dancard32/spotify-player/assets/Blank_3D_Render.png

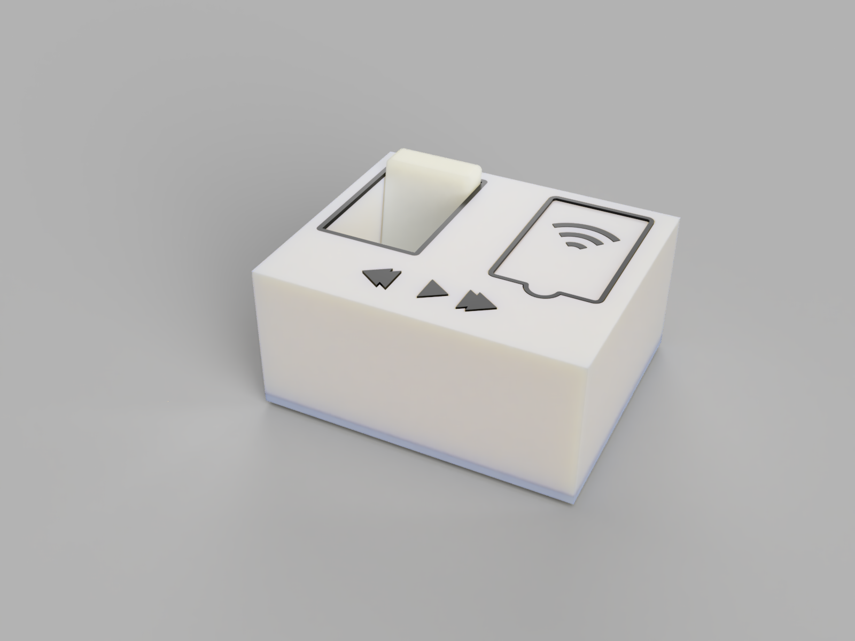
assets/Blank_3D_Render.png
