dancard32/spotify-player/assets/coverPhoto.png

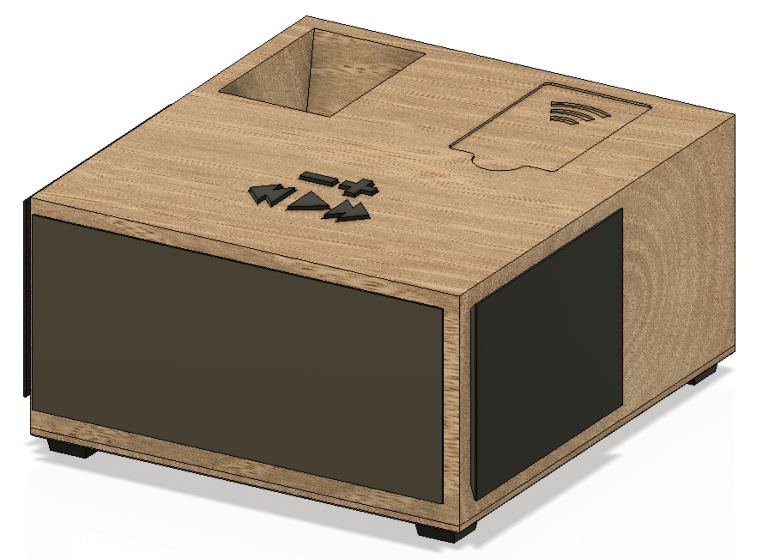
assets/coverPhoto.png
