dancard32/spotify-player/images/cards/cover_art/.png

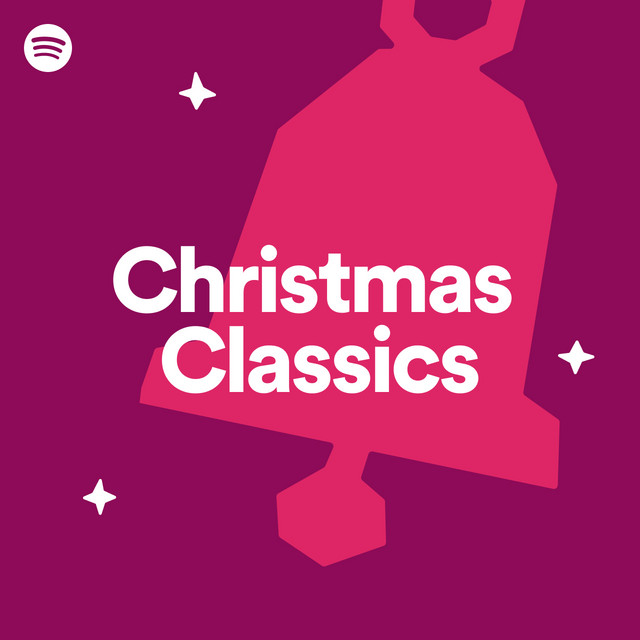
images/cards/cover_art/.png
