dancard32/spotify-player/images/cards/cover_art/African Heat.png

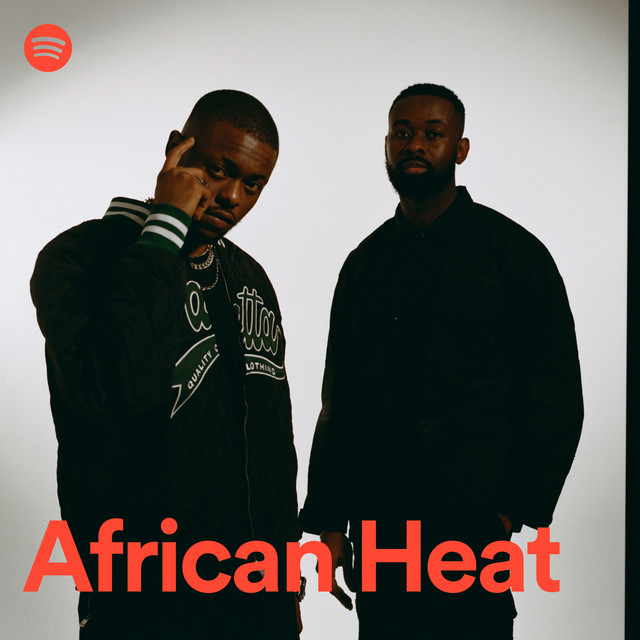
images/cards/cover_art/African Heat.png
