dancard32/spotify-player/images/cards/cover_art/All Out 60s.png

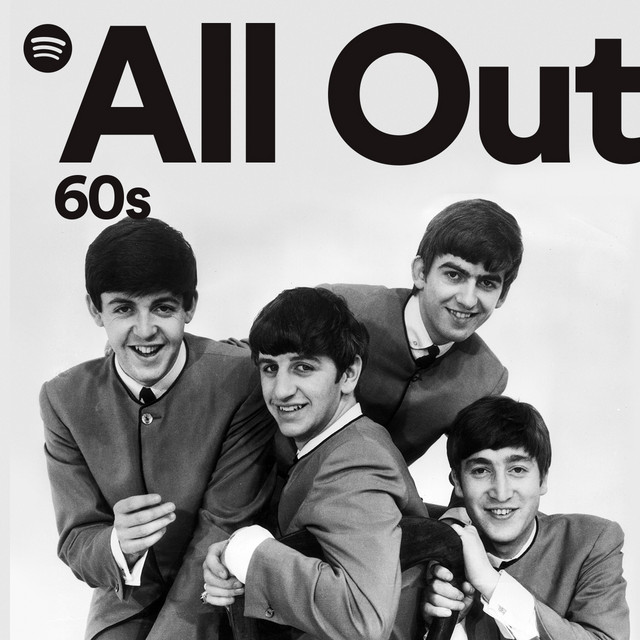
images/cards/cover_art/All Out 60s.png
