dancard32/spotify-player/images/cards/cover_art/All Out 70s.png

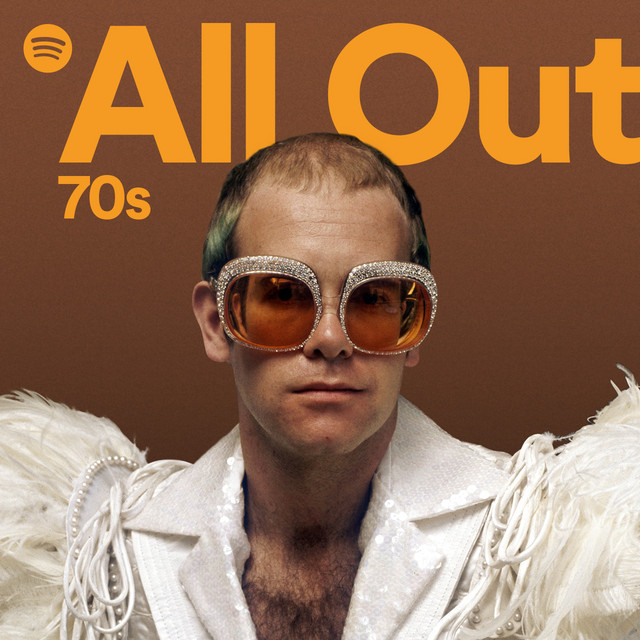
images/cards/cover_art/All Out 70s.png
