dancard32/spotify-player/images/cards/cover_art/All Out 90s.png

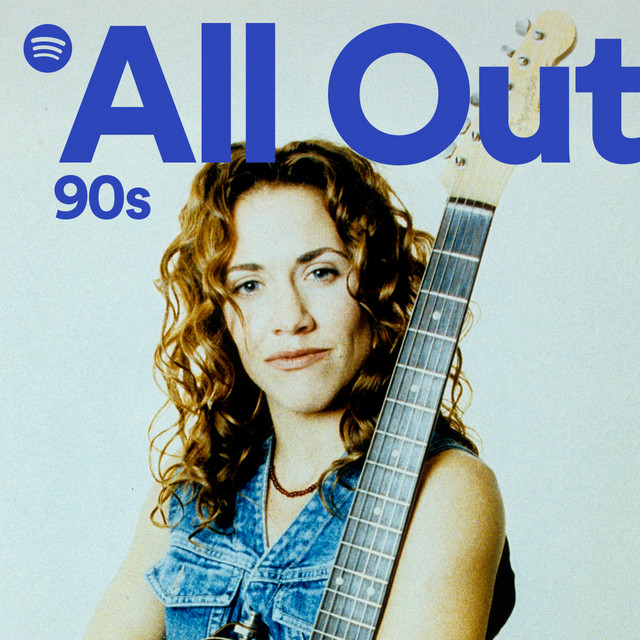
images/cards/cover_art/All Out 90s.png
