dancard32/spotify-player/images/cards/cover_art/All Out 2000s.png

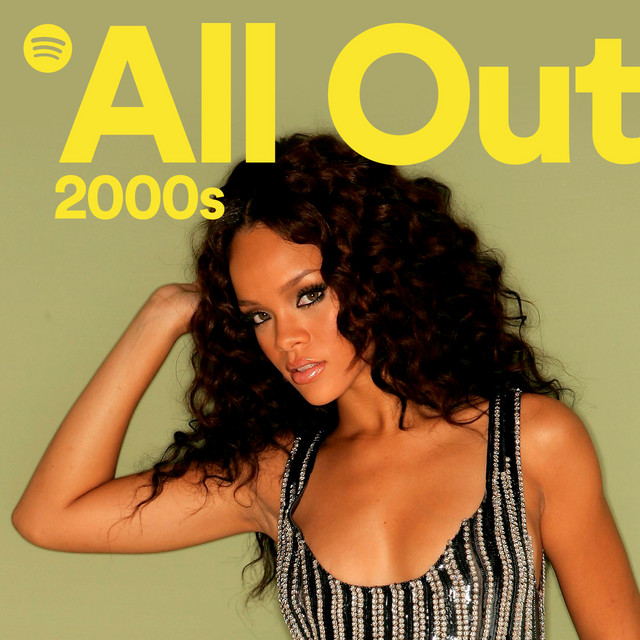
images/cards/cover_art/All Out 2000s.png
