dancard32/spotify-player/images/cards/cover_art/Atmospheric Sci-Fi.png

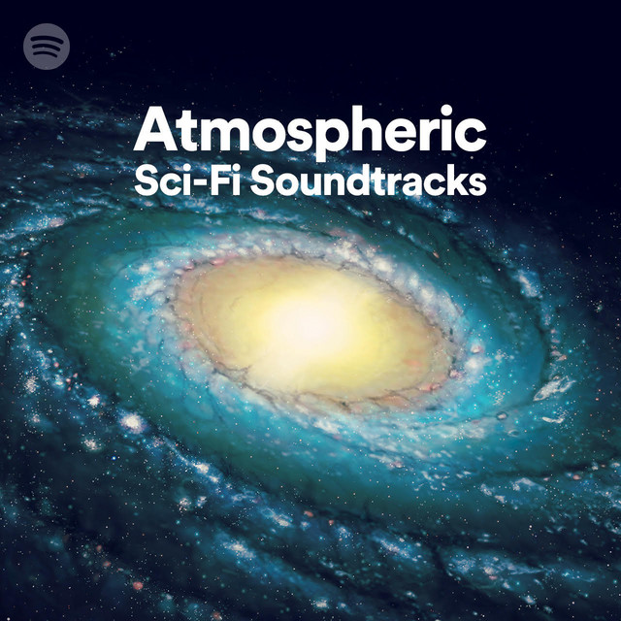
images/cards/cover_art/Atmospheric Sci-Fi.png
