dancard32/spotify-player/images/cards/cover_art/Chilled R&B.png

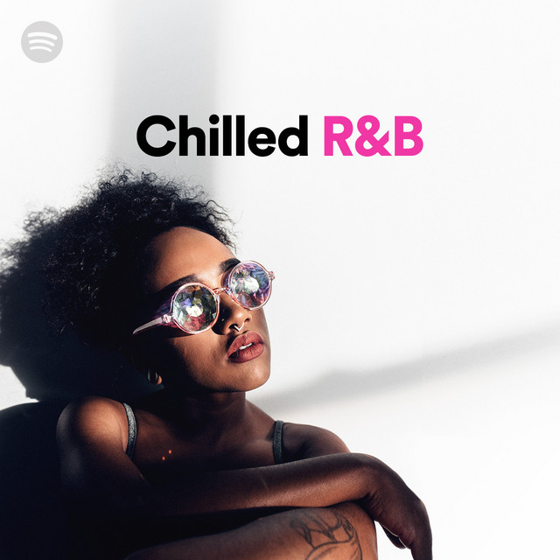
images/cards/cover_art/Chilled R&B.png
