dancard32/spotify-player/images/cards/cover_art/Country .png

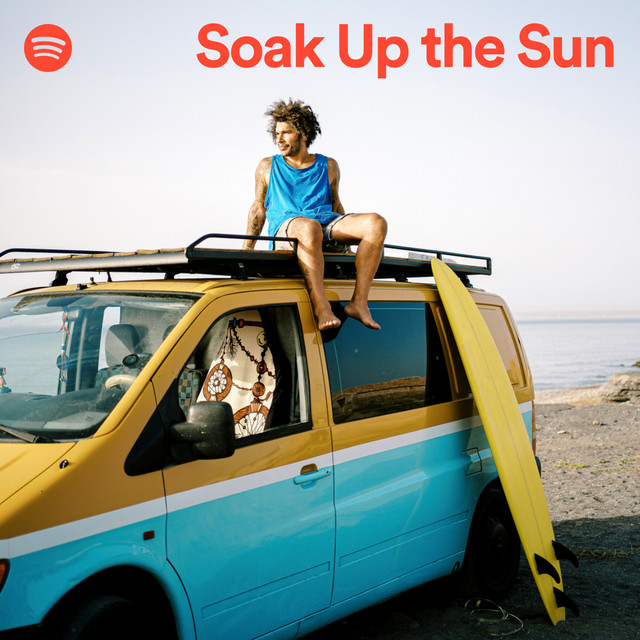
images/cards/cover_art/Country .png
