dancard32/spotify-player/images/cards/cover_art/Funk Outta Here.png

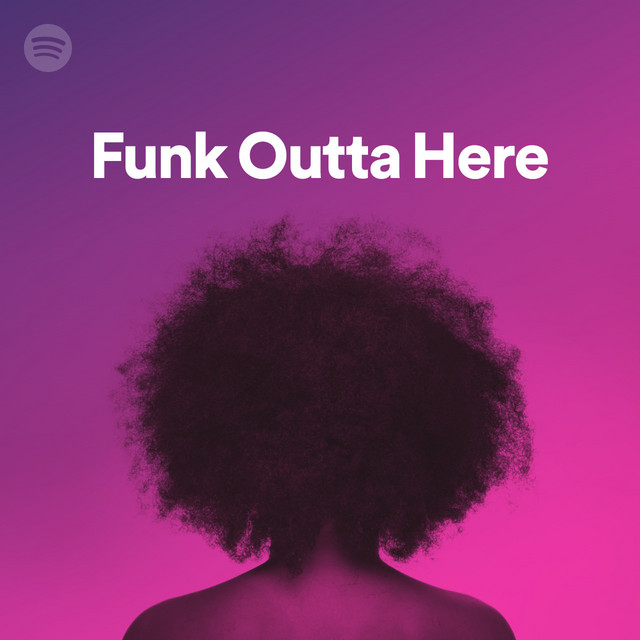
images/cards/cover_art/Funk Outta Here.png
