dancard32/spotify-player/images/cards/cover_art/Hip Hop Mix.png

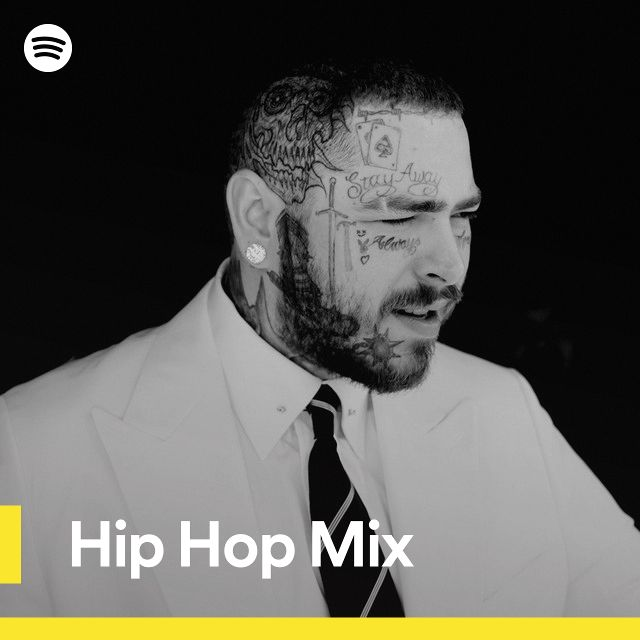
images/cards/cover_art/Hip Hop Mix.png
