dancard32/spotify-player/images/cards/cover_art/Kurzgesagt in a nutshell.png

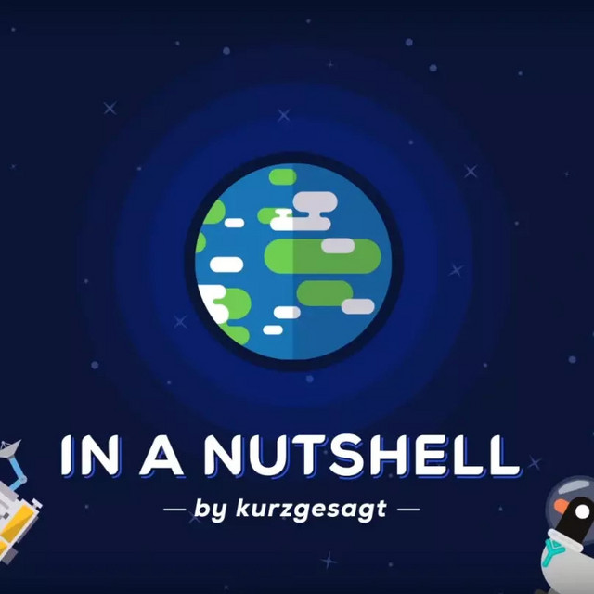
images/cards/cover_art/Kurzgesagt in a nutshell.png
