dancard32/spotify-player/images/cards/cover_art/Late Night Jazz.png

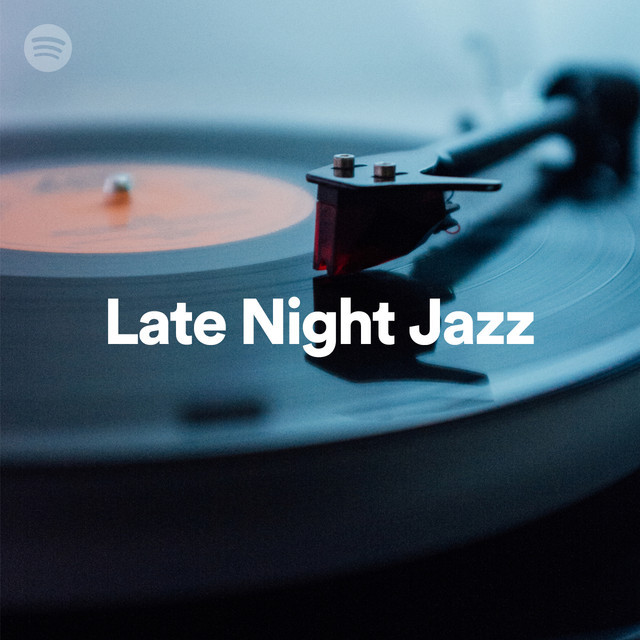
images/cards/cover_art/Late Night Jazz.png
