dancard32/spotify-player/images/cards/cover_art/lofi hip hop music.png

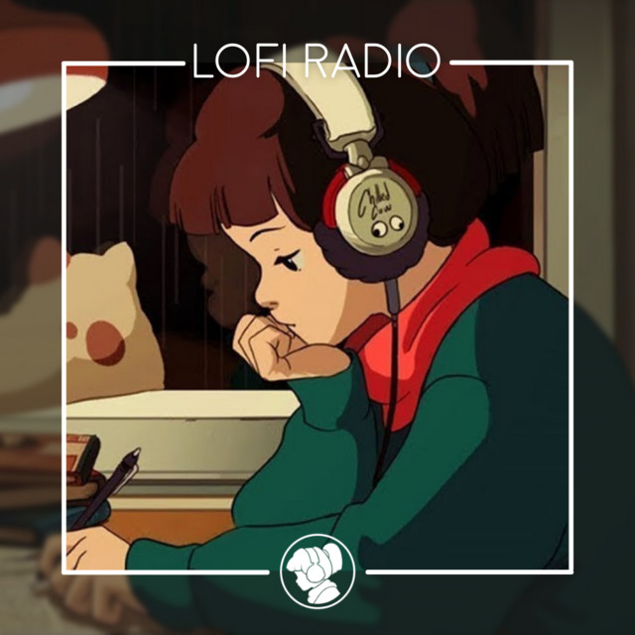
images/cards/cover_art/lofi hip hop music.png
