dancard32/spotify-player/images/cards/cover_art/New Music Friday.png

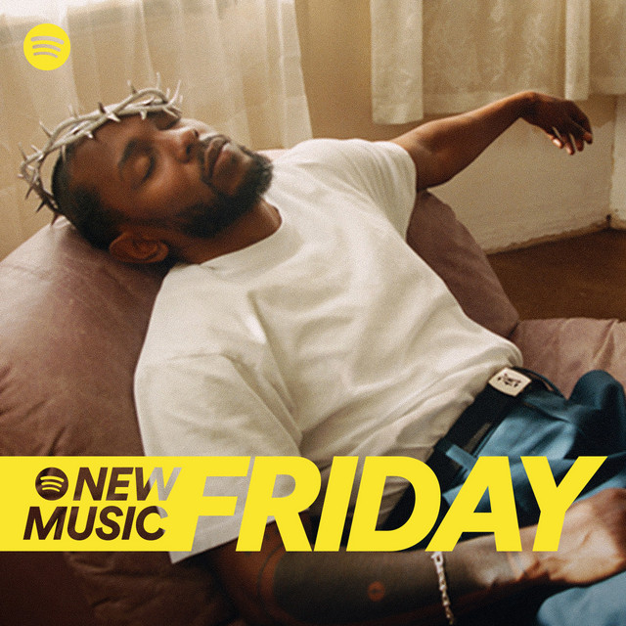
images/cards/cover_art/New Music Friday.png
