dancard32/spotify-player/images/cards/cover_art/Party Mix.png

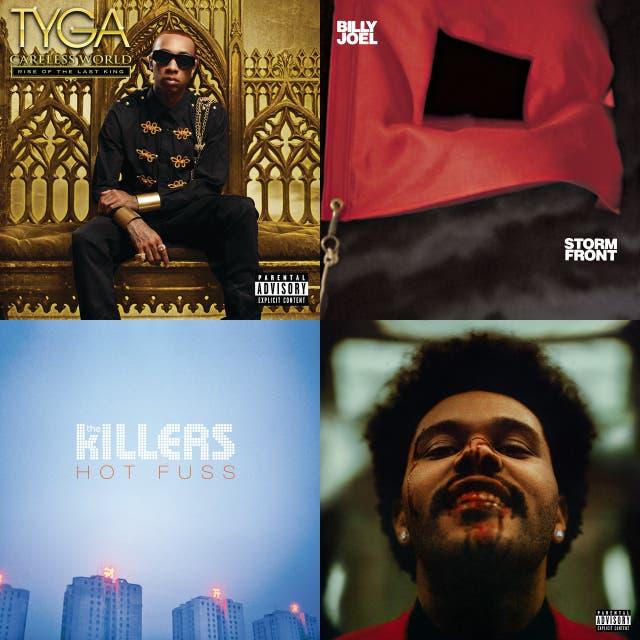
images/cards/cover_art/Party Mix.png
