dancard32/spotify-player/images/cards/cover_art/R&B Mix.png

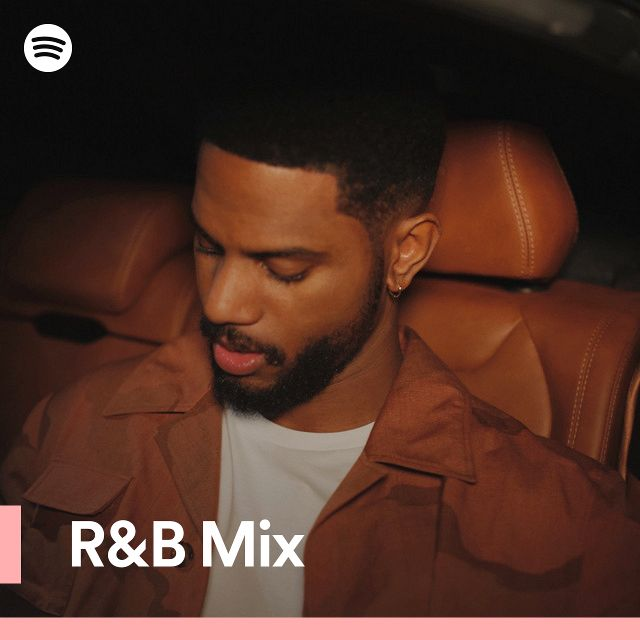
images/cards/cover_art/R&B Mix.png
