dancard32/spotify-player/images/cards/cover_art/Rap.png

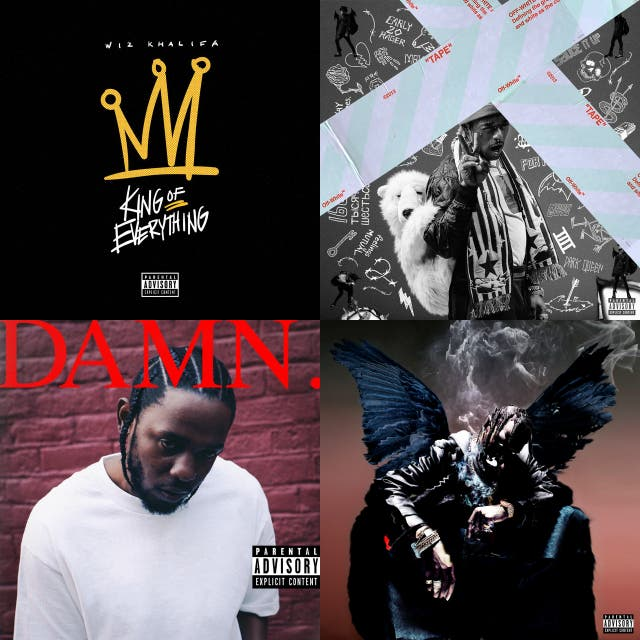
images/cards/cover_art/Rap.png
