dancard32/spotify-player/images/cards/cover_art/RapCaviar.png

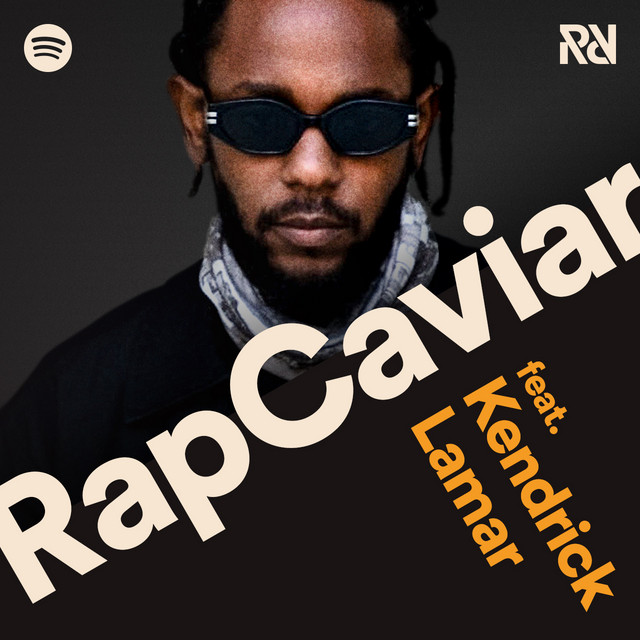
images/cards/cover_art/RapCaviar.png
