dancard32/spotify-player/images/cards/cover_art/Road Trips.png

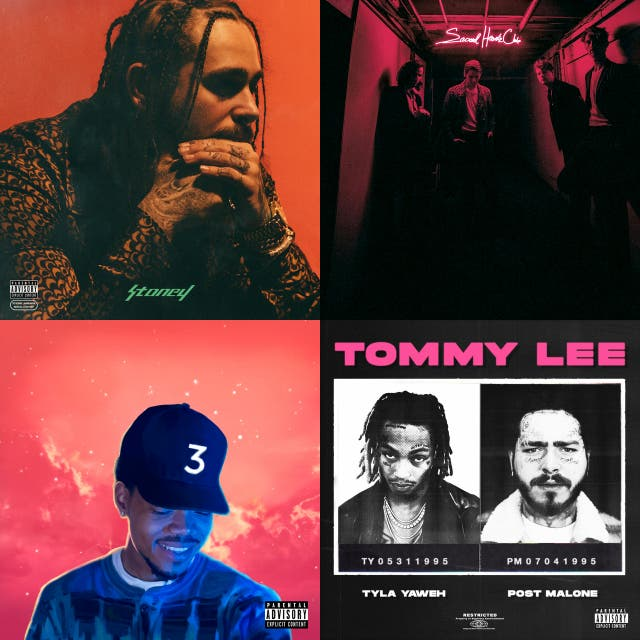
images/cards/cover_art/Road Trips.png
