dancard32/spotify-player/images/cards/cover_art/Rock Classics.png

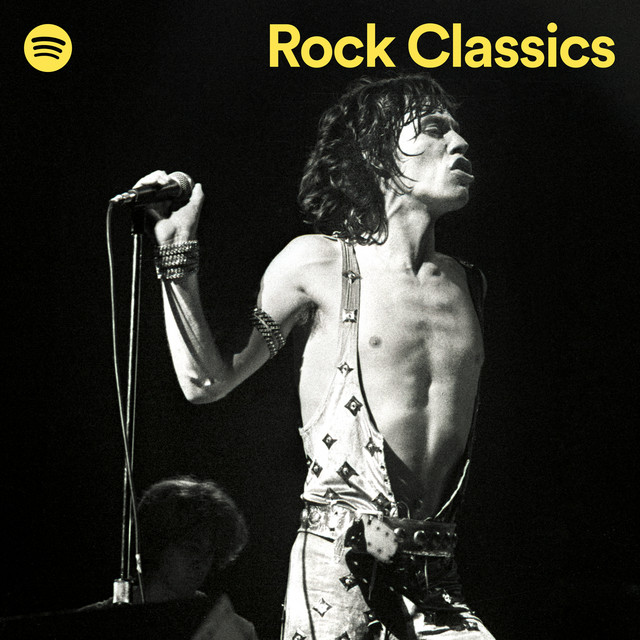
images/cards/cover_art/Rock Classics.png
