dancard32/spotify-player/images/cards/cover_art/Rock Party.png

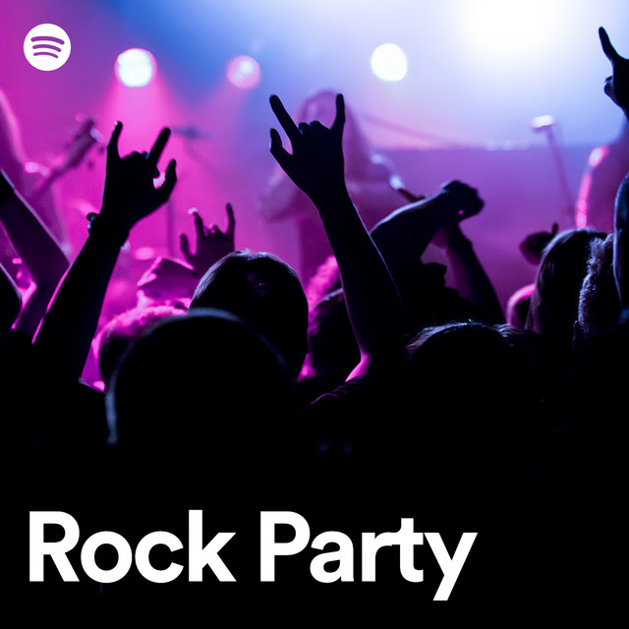
images/cards/cover_art/Rock Party.png
