dancard32/spotify-player/images/cards/cover_art/Soft Pop Hits.png

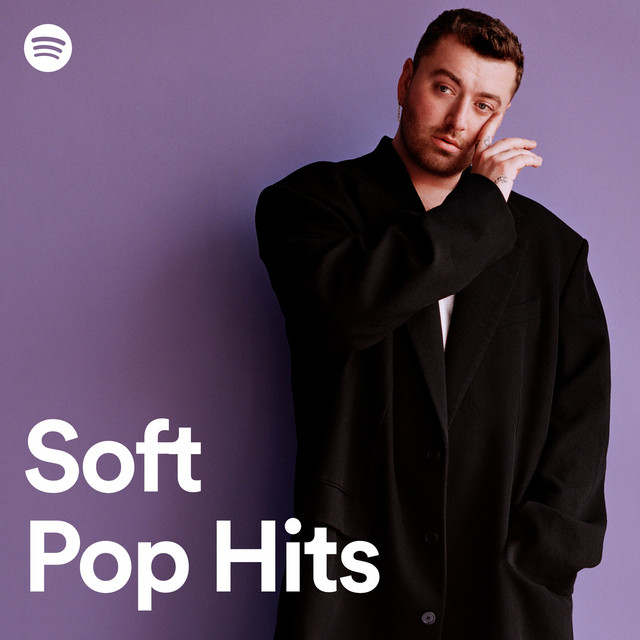
images/cards/cover_art/Soft Pop Hits.png
