dancard32/spotify-player/images/cards/cover_art/Soul Revived.png

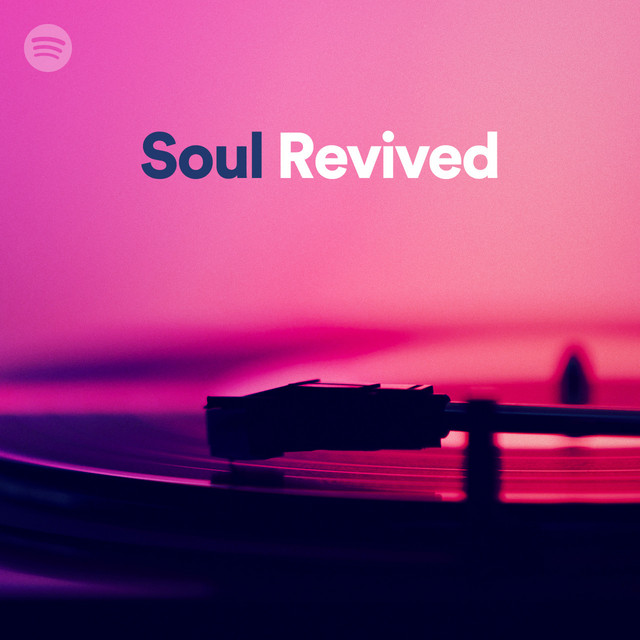
images/cards/cover_art/Soul Revived.png
