dancard32/spotify-player/images/cards/cover_art/spikeball w the boys.png

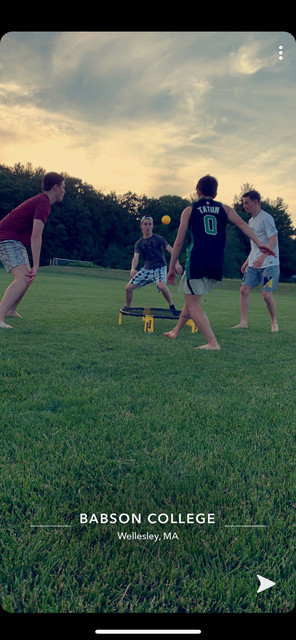
images/cards/cover_art/spikeball w the boys.png
