dancard32/spotify-player/images/cards/cover_art/Spread the Gospel.png

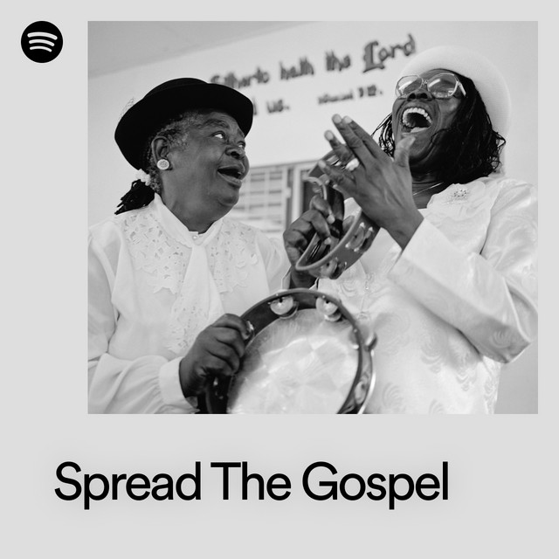
images/cards/cover_art/Spread the Gospel.png
