dancard32/spotify-player/images/cards/cover_art/Today's Top Hits.png

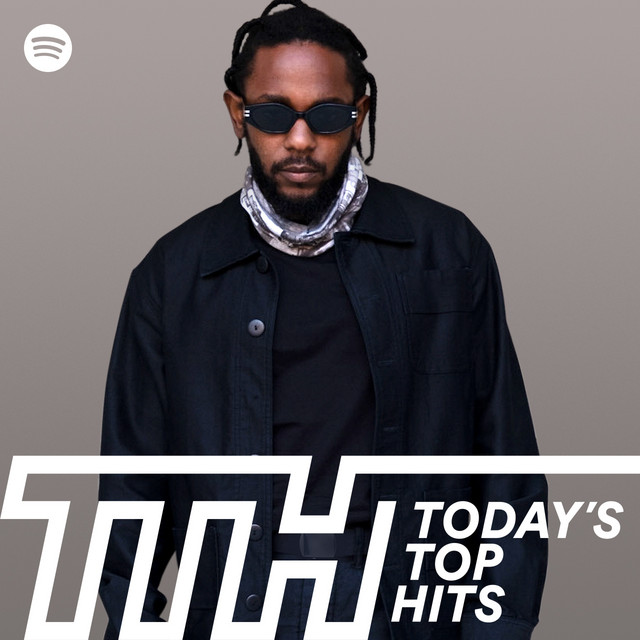
images/cards/cover_art/Today's Top Hits.png
