dancard32/spotify-player/images/cards/cover_art/Viva Latino.png

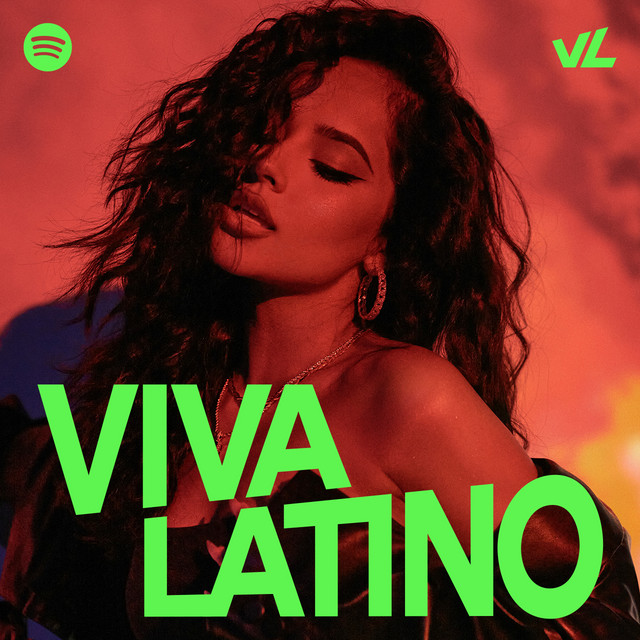
images/cards/cover_art/Viva Latino.png
