dancard32/spotify-player/images/cards/cover_art/We Everywhere.png

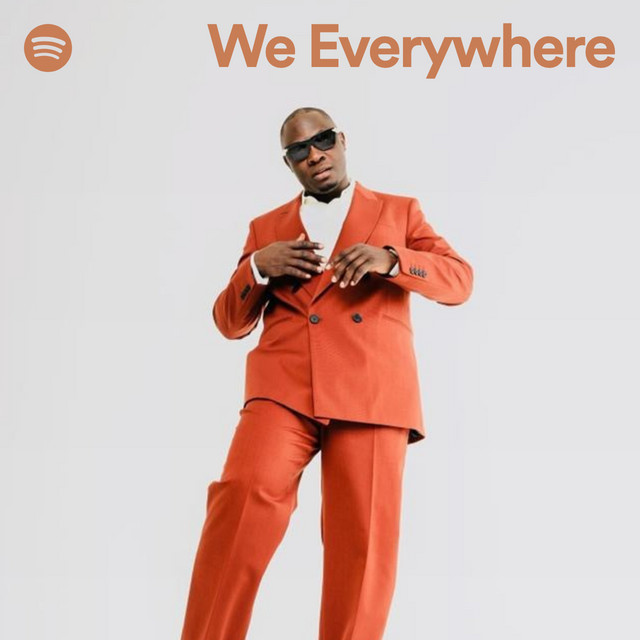
images/cards/cover_art/We Everywhere.png
