dancard32/spotify-player/images/cards/cover_art/Wine & Dine.png

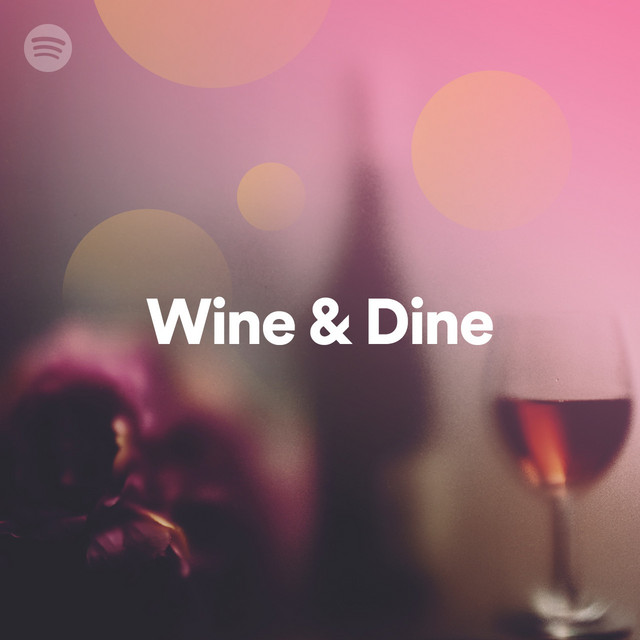
images/cards/cover_art/Wine & Dine.png
