dancard32/spotify-player/images/pages/page_0.png

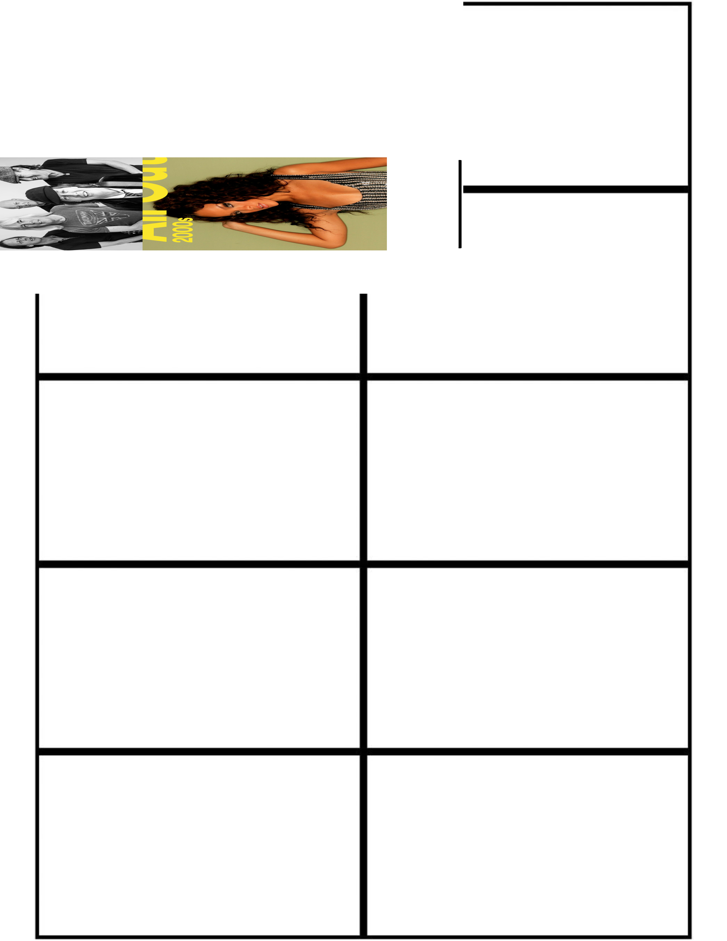
images/pages/page_0.png
