dancard32/spotify-player/images/pages/page_1.png

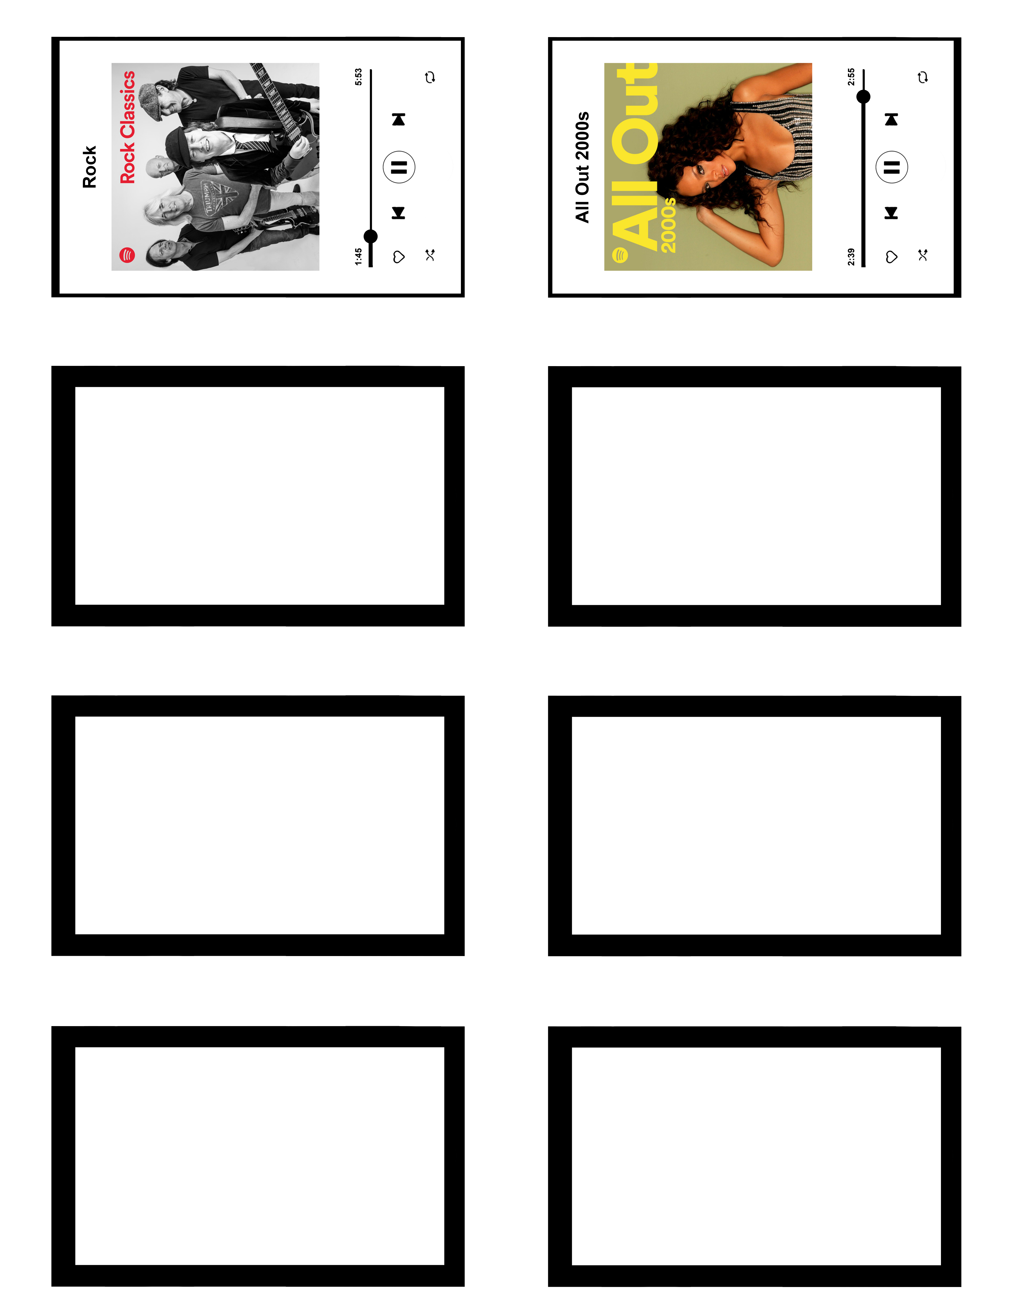
images/pages/page_1.png
