dancard32/spotify-player/images/pages/page_4.png

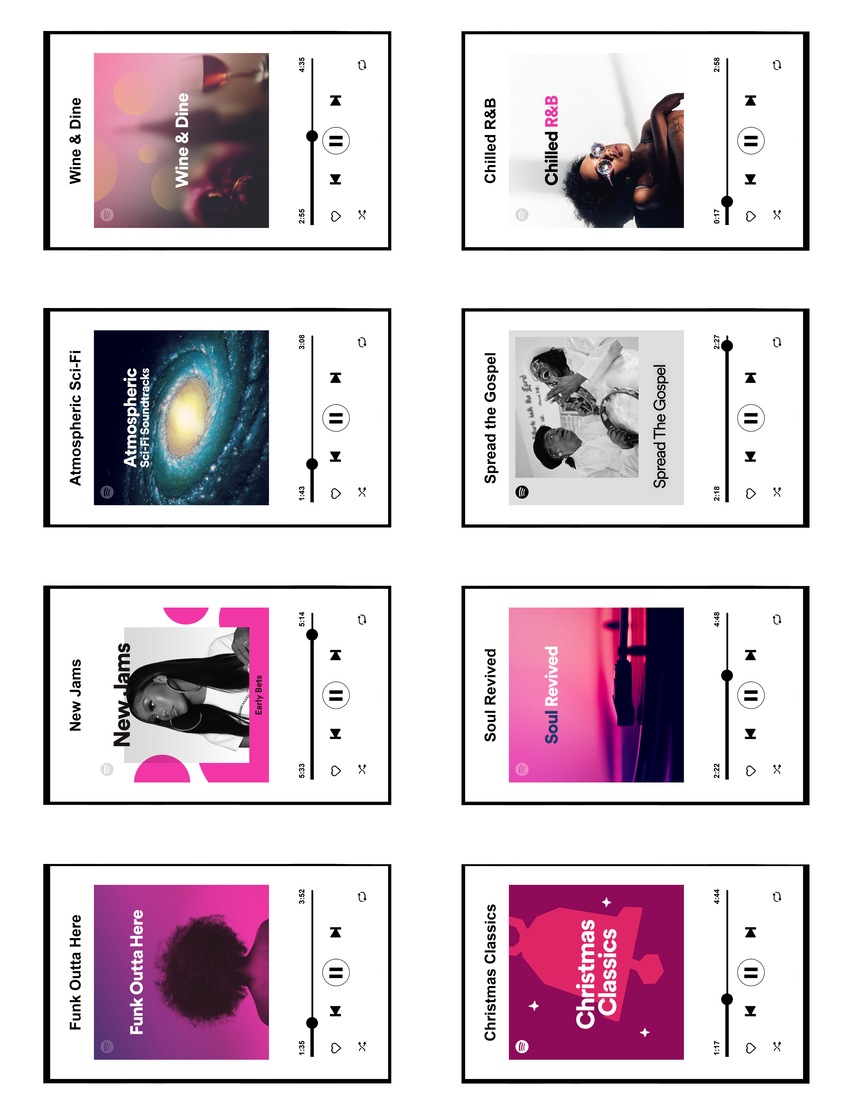
images/pages/page_4.png
